ntava001/drone-delivery-device/models/roller base.SLDPRT

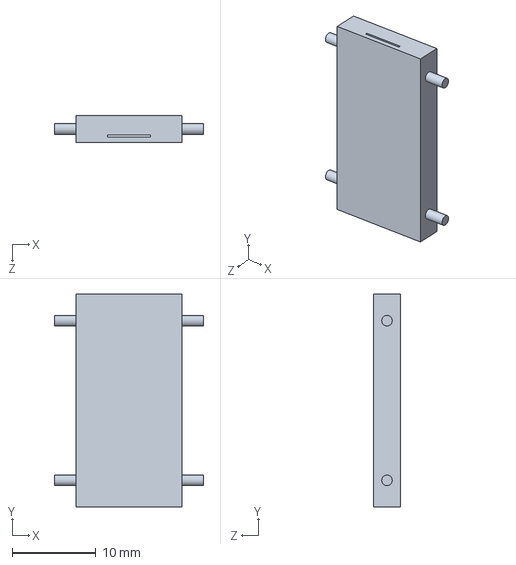
[picture p47: CAD file, 2022-05-28]
models/roller base.SLDPRT
17.8 x 25.4 x 3.17 mm
