ntava001/drone-delivery-device/models/belt chain part.SLDPRT

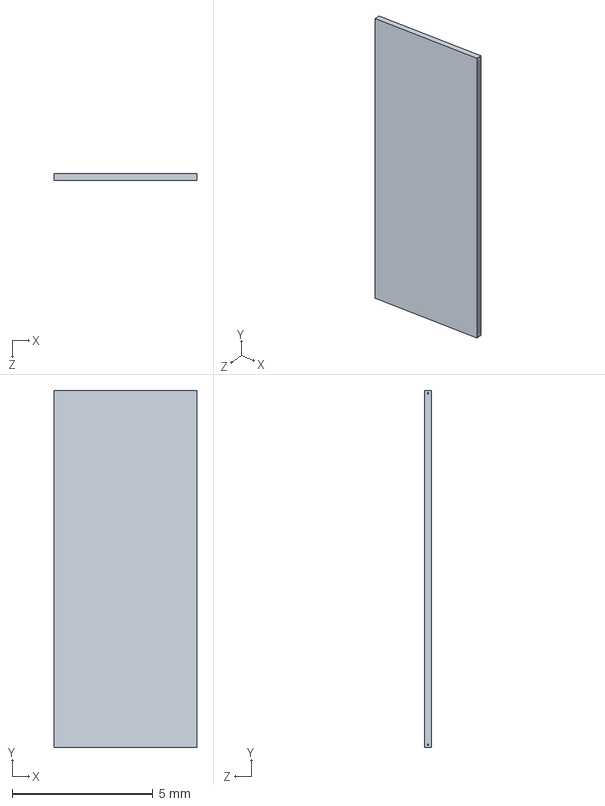
[picture p48: CAD file, 2022-05-28]
models/belt chain part.SLDPRT
5.08 x 12.7 x 0.254 mm
