ntava001/drone-delivery-device/models/holder vertical shaft.SLDPRT

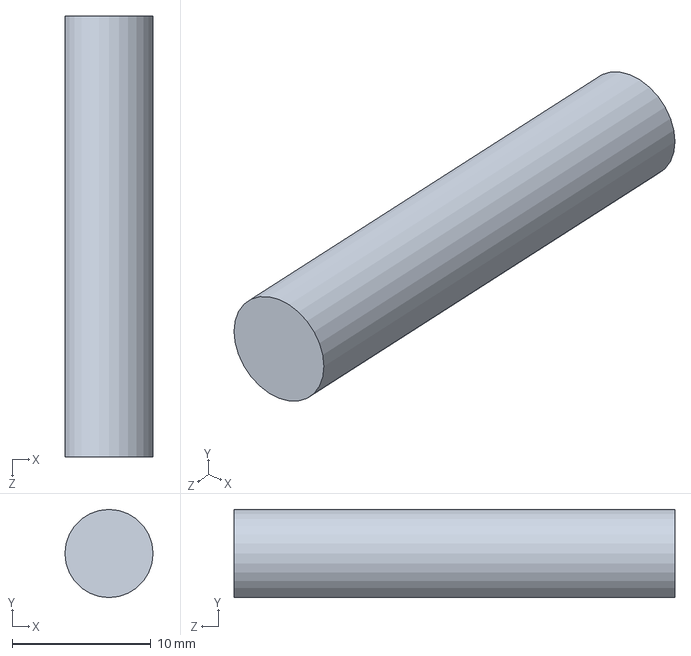
[picture p49: CAD file, 2022-05-28]
models/holder vertical shaft.SLDPRT
6.35 x 6.35 x 31.8 mm
