ntava001/drone-delivery-device/models/battery plate bottom.SLDPRT

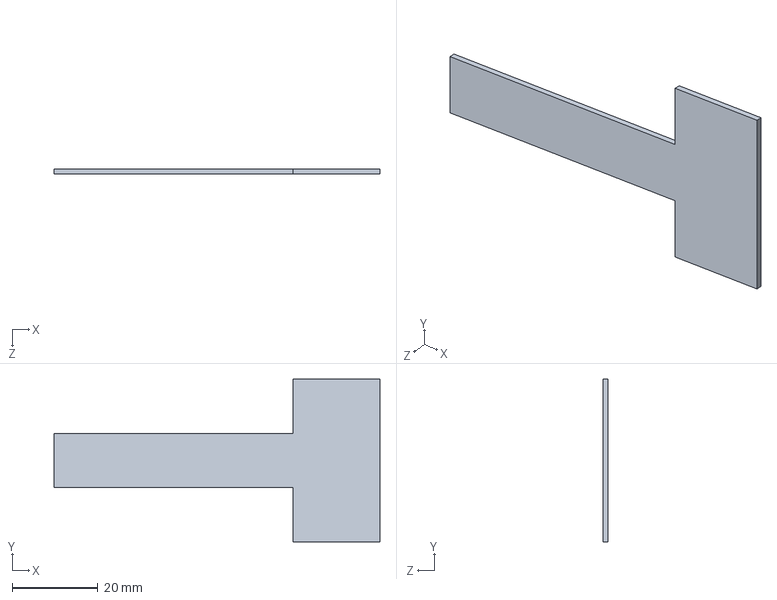
[picture p50: CAD file, 2022-05-28]
models/battery plate bottom.SLDPRT
76.2 x 38.1 x 1.27 mm
