ntava001/drone-delivery-device/models/stepper motor.SLDPRT

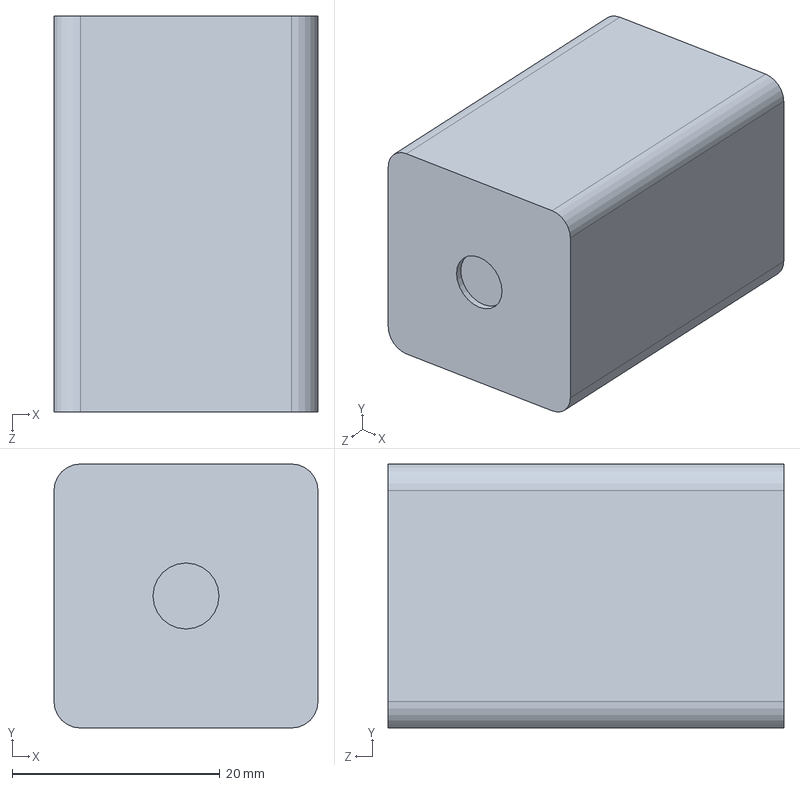
[picture p51: CAD file, 2022-05-28]
models/stepper motor.SLDPRT
25.4 x 25.4 x 38.1 mm
