ntava001/drone-delivery-device/models/pulley.SLDPRT

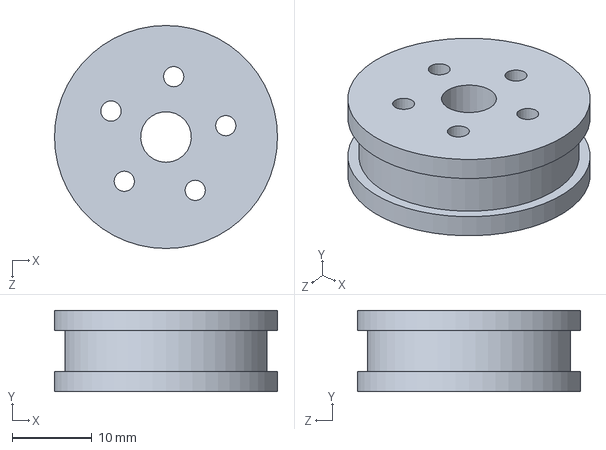
[picture p52: CAD file, 2022-05-28]
models/pulley.SLDPRT
27.9 x 10.2 x 27.9 mm
