ntava001/drone-delivery-device/models/battery plate.SLDPRT

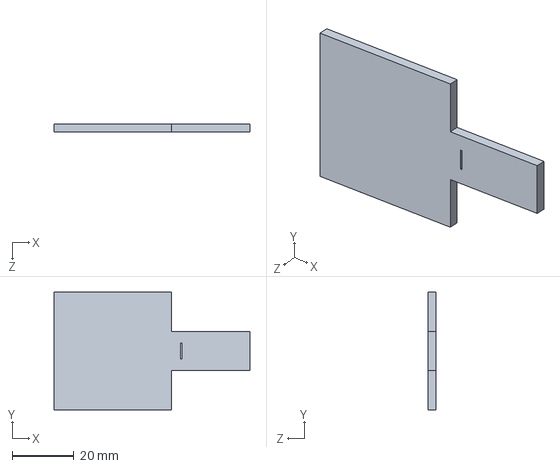
[picture p53: CAD file, 2022-05-28]
models/battery plate.SLDPRT
63.5 x 38.1 x 2.54 mm
