ntava001/drone-delivery-device/models/motor shaft.SLDPRT

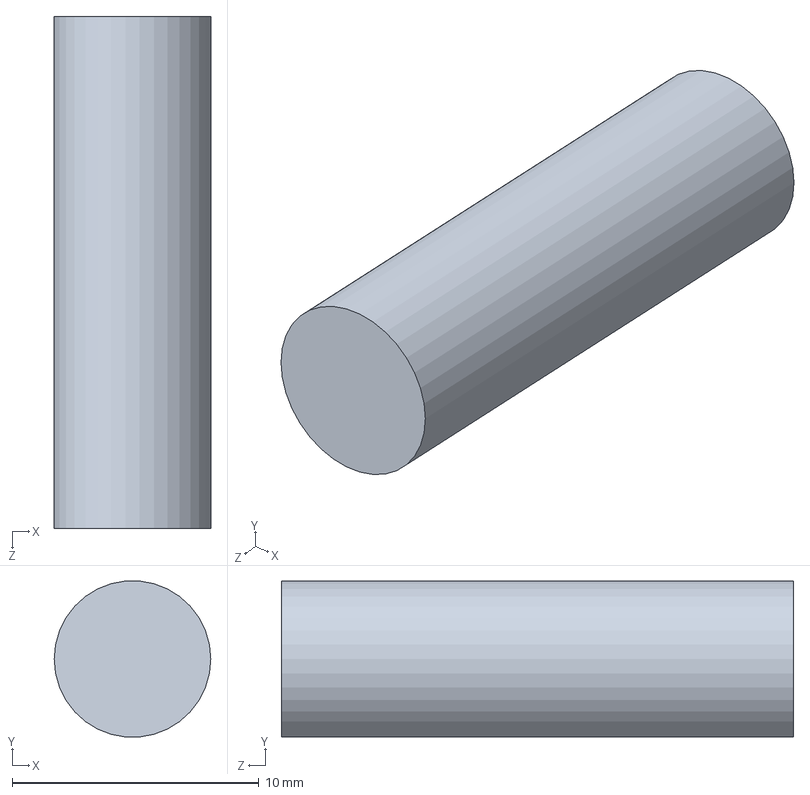
[picture p54: CAD file, 2022-05-28]
models/motor shaft.SLDPRT
6.35 x 6.32 x 20.8 mm
