ntava001/drone-delivery-device/models/Part2.SLDPRT

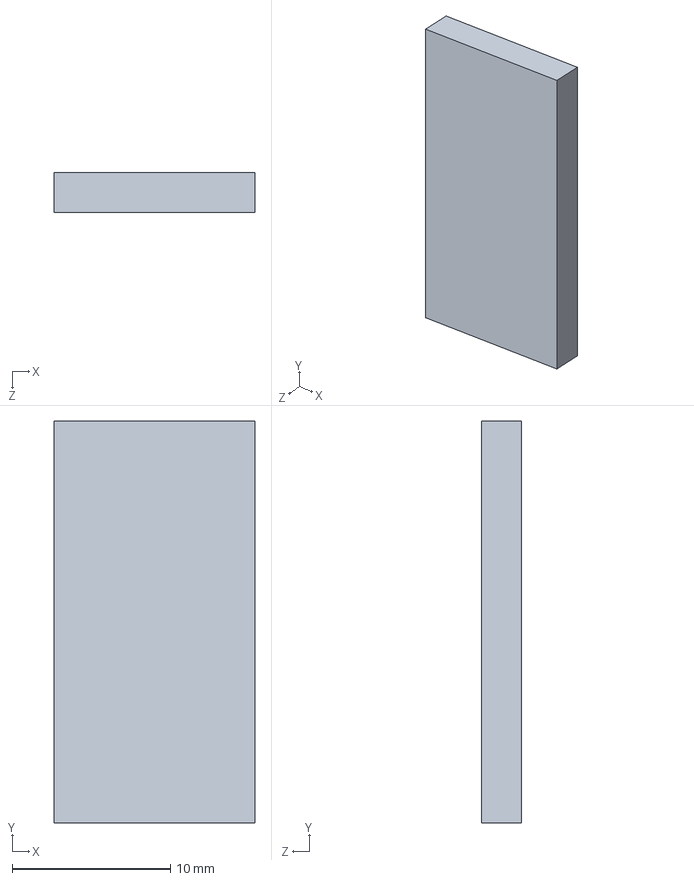
[picture p55: CAD file, 2022-05-28]
models/Part2.SLDPRT
12.7 x 25.4 x 2.54 mm
