ntava001/drone-delivery-device/models/door2.SLDPRT

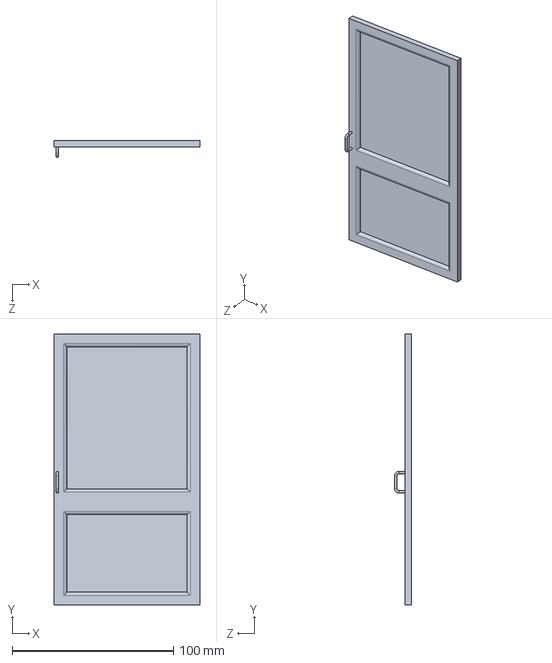
[picture p56: CAD file, 2022-05-28]
models/door2.SLDPRT
90.4 x 168.0 x 10.4 mm
