ntava001/drone-delivery-device/models/medium Glass.SLDPRT

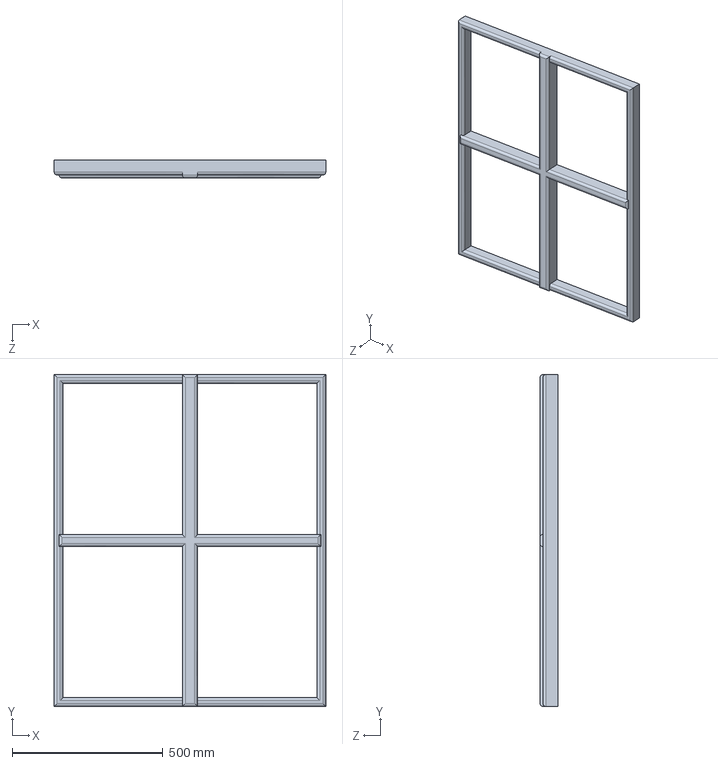
[picture p57: CAD file, 2022-05-28]
models/medium Glass.SLDPRT
900.0 x 1100.0 x 60.0 mm
