ntava001/drone-delivery-device/models/med glass.SLDPRT

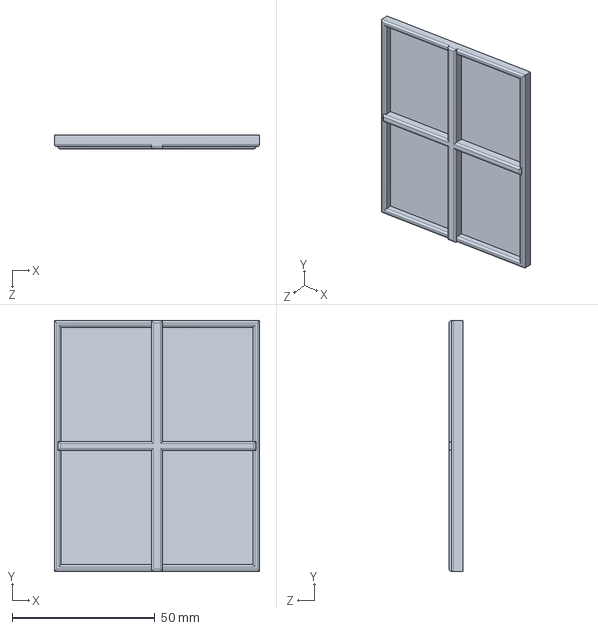
[picture p58: CAD file, 2022-05-28]
models/med glass.SLDPRT
72.0 x 88.0 x 4.80 mm
