ntava001/drone-delivery-device/models/battery cage.SLDPRT

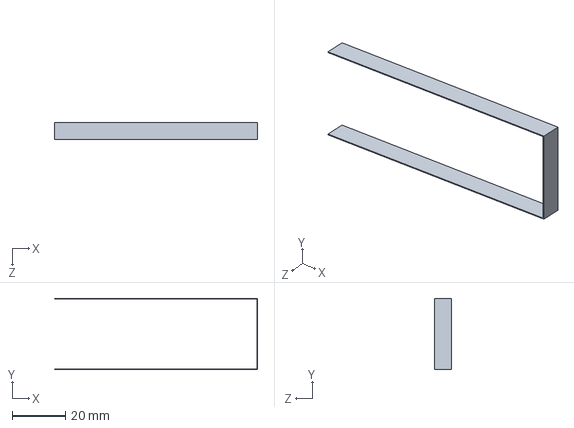
[picture p59: CAD file, 2022-05-28]
models/battery cage.SLDPRT
76.2 x 26.7 x 6.35 mm
