ntava001/drone-delivery-device/models/Glass.SLDPRT

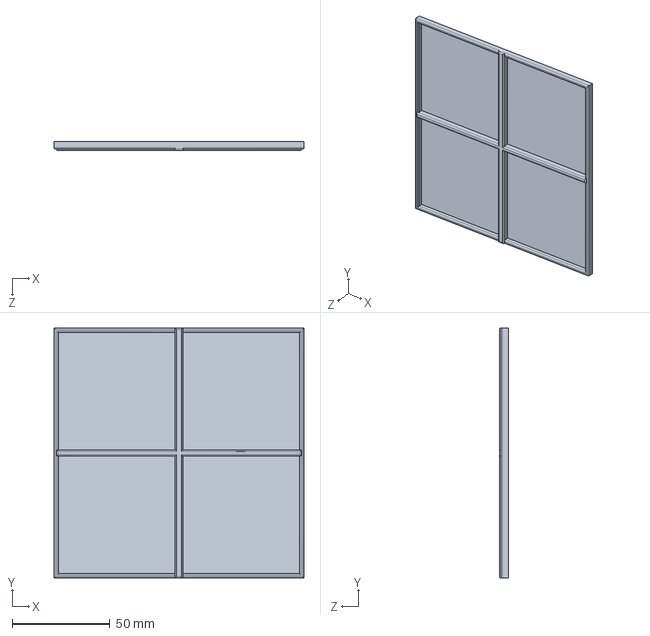
[picture p60: CAD file, 2022-05-28]
models/Glass.SLDPRT
128.0 x 128.0 x 4.80 mm
