ntava001/drone-delivery-device/models/pulley holder.SLDPRT

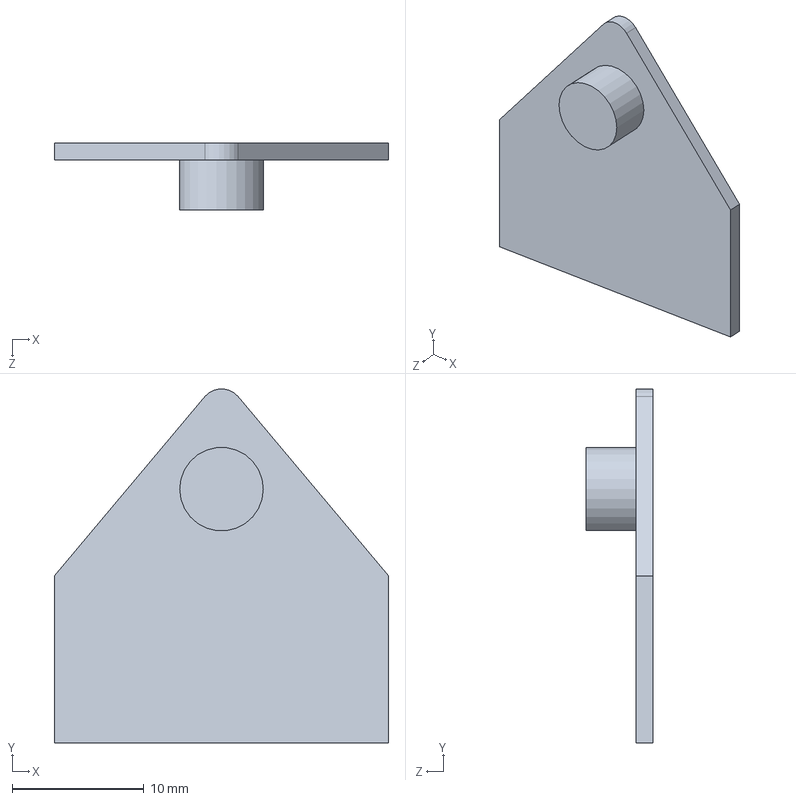
[picture p61: CAD file, 2022-05-28]
models/pulley holder.SLDPRT
25.4 x 26.9 x 5.08 mm
