ntava001/drone-delivery-device/models/Small Glass.SLDPRT

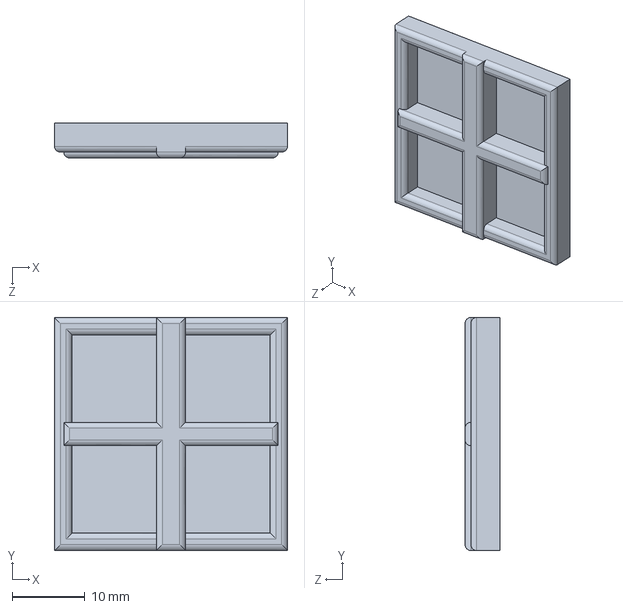
[picture p62: CAD file, 2022-05-28]
models/Small Glass.SLDPRT
32.0 x 32.0 x 4.80 mm
