ntava001/drone-delivery-device/models/Cardboard Box.SLDPRT

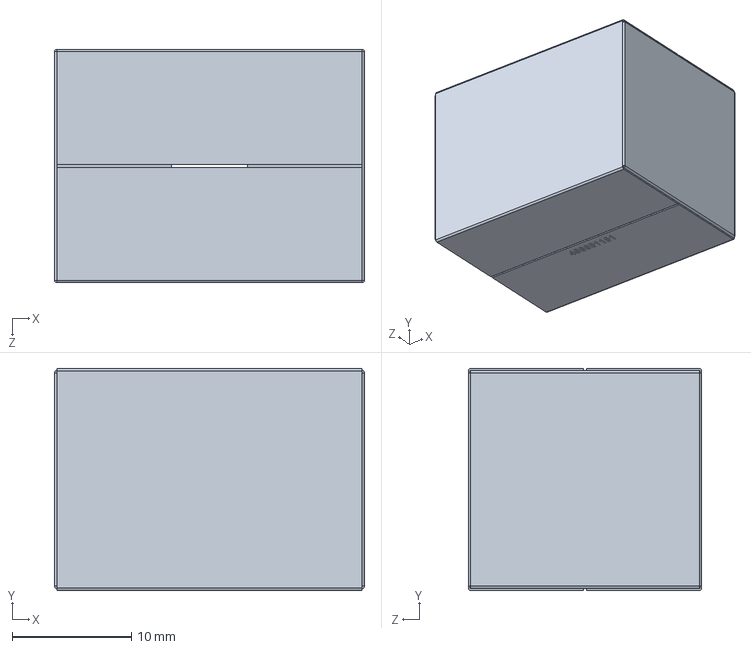
[picture p63: CAD file, 2022-05-28]
models/Cardboard Box.SLDPRT
26.0 x 18.6 x 19.6 mm
