ntava001/drone-delivery-device/models/damper.SLDPRT

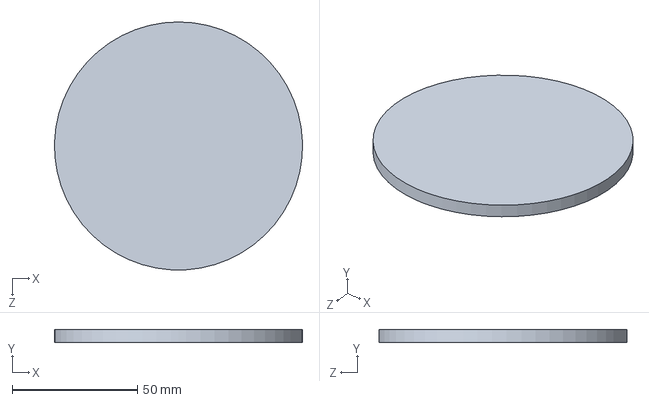
[picture p64: CAD file, 2022-05-28]
models/damper.SLDPRT
99.0 x 5.08 x 99.1 mm
