ntava001/drone-delivery-device/models/roller slide.SLDPRT

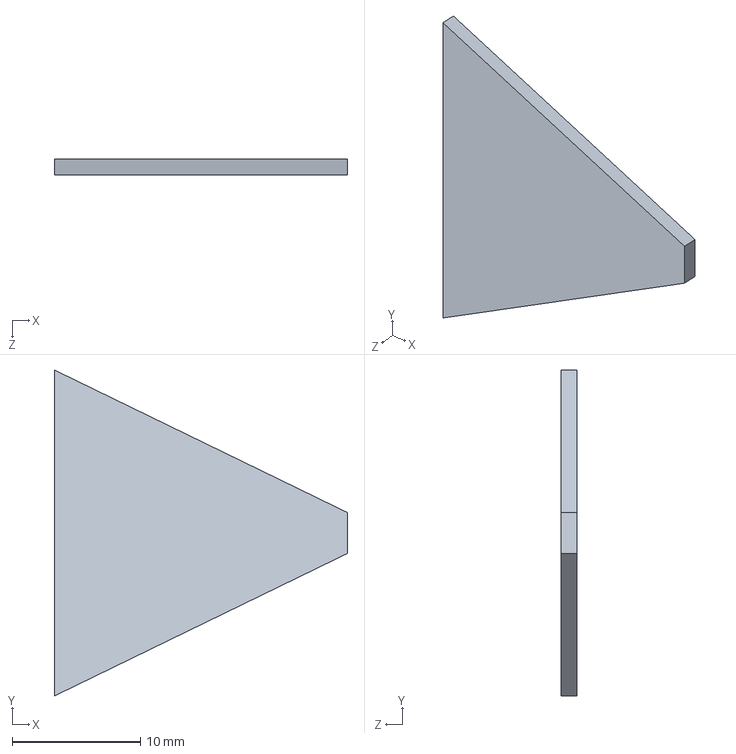
[picture p65: CAD file, 2022-05-28]
models/roller slide.SLDPRT
22.8 x 25.4 x 1.27 mm
